vtimuchen-lab/dual-spark-4u/docs/drawings/panel_fp5.png

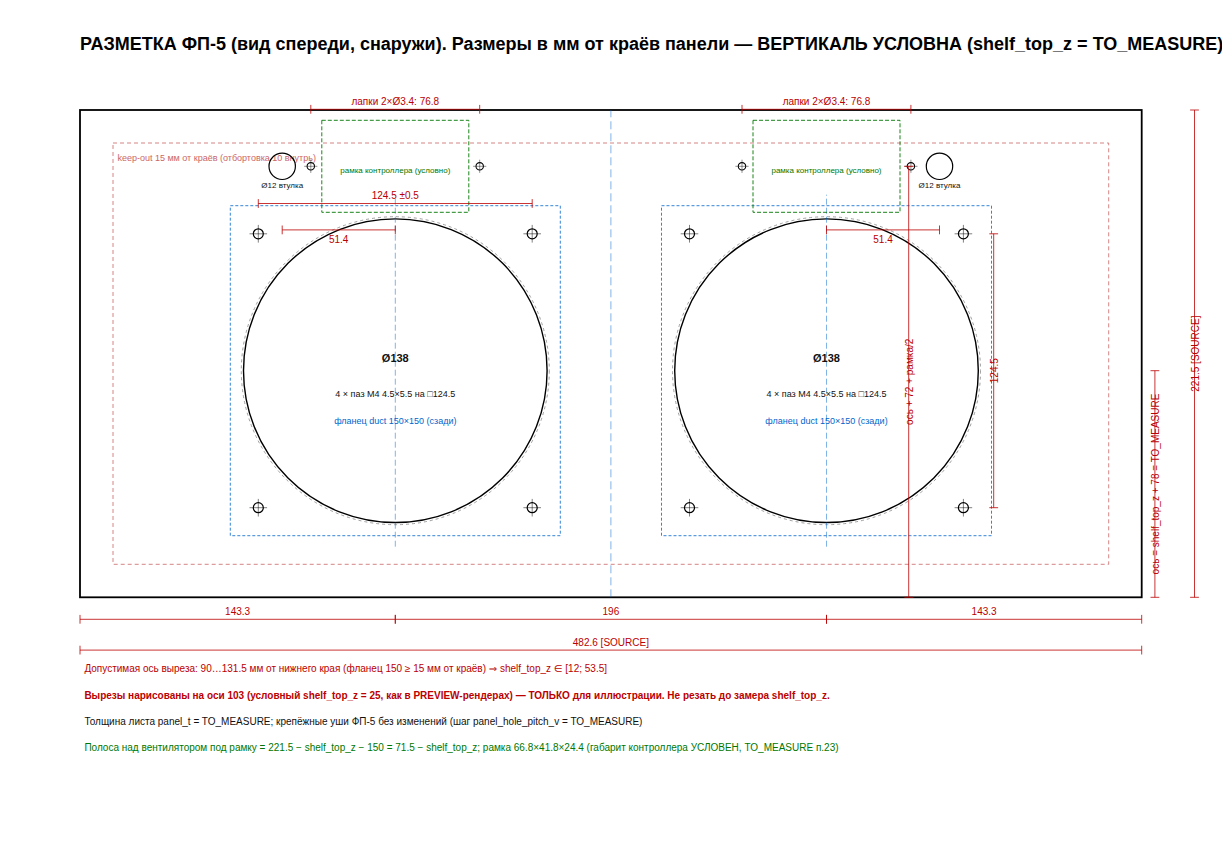
docs/drawings/panel_fp5.png
