vtimuchen-lab/dual-spark-4u/docs/drawings/side_view.png

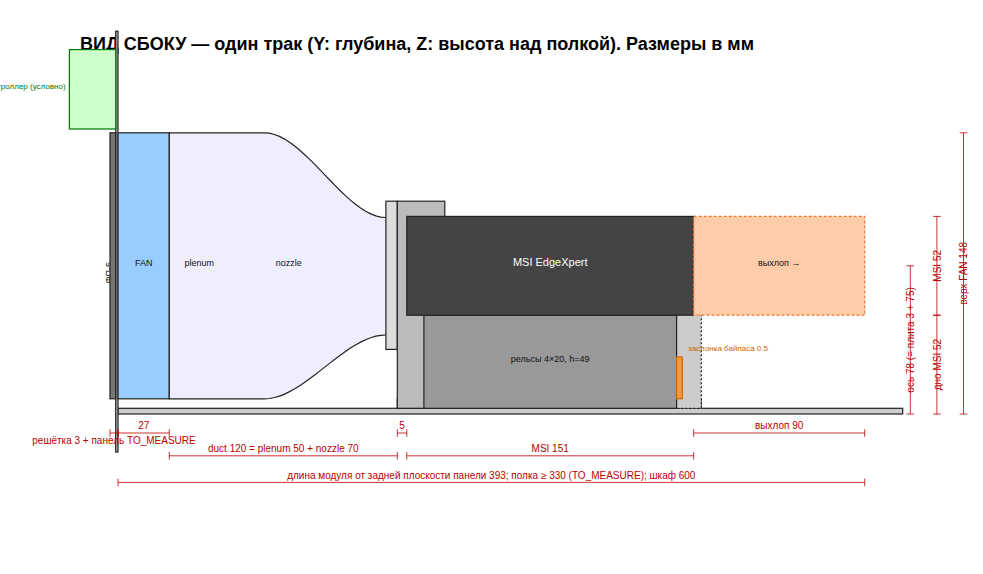
docs/drawings/side_view.png
