vtimuchen-lab/dual-spark-4u/docs/drawings/top_view.png

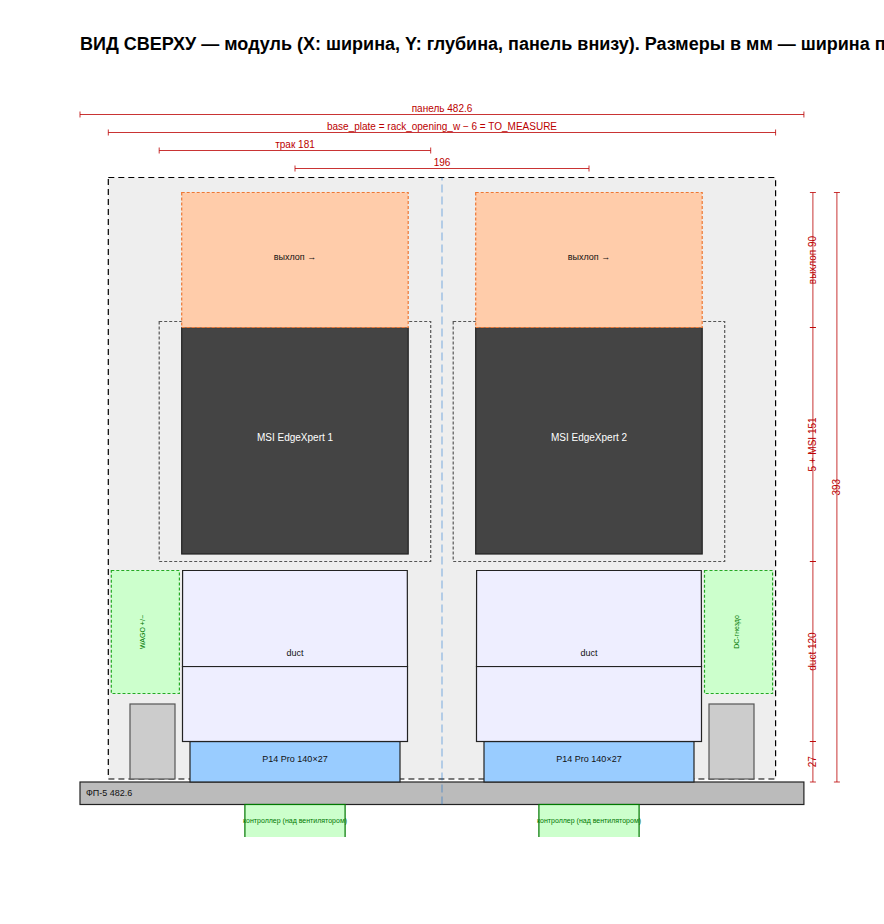
docs/drawings/top_view.png
