vtimuchen-lab/dual-spark-4u/docs/renders/duct_section_PREVIEW.png

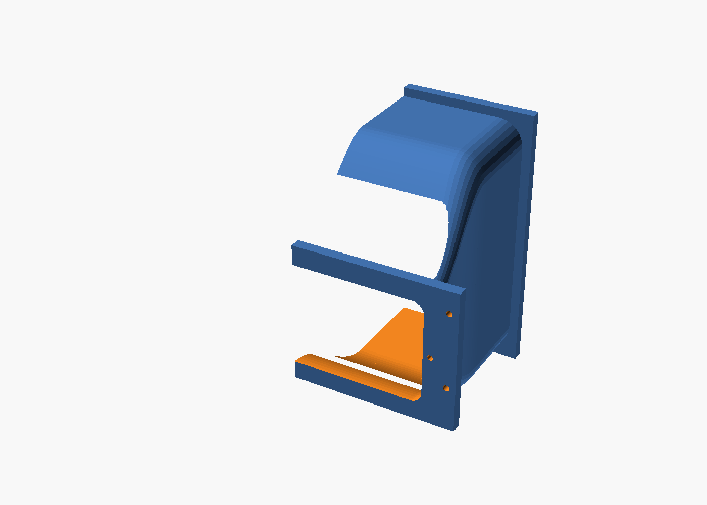
docs/renders/duct_section_PREVIEW.png
