vtimuchen-lab/dual-spark-4u/docs/renders/exploded_PREVIEW.png

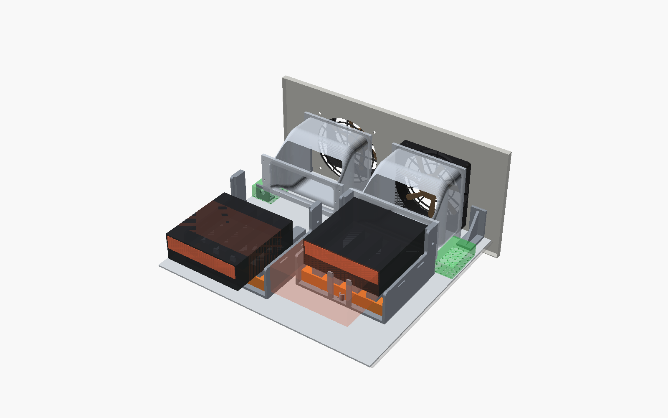
docs/renders/exploded_PREVIEW.png
