vtimuchen-lab/dual-spark-4u/docs/renders/holder_PREVIEW.png

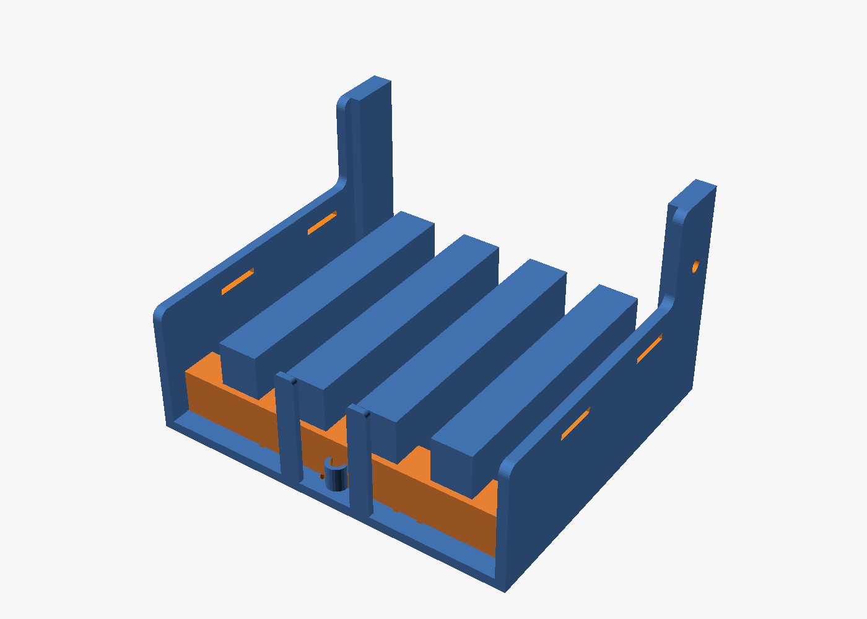
docs/renders/holder_PREVIEW.png
