vtimuchen-lab/dual-spark-4u/docs/renders/module_top_PREVIEW.png

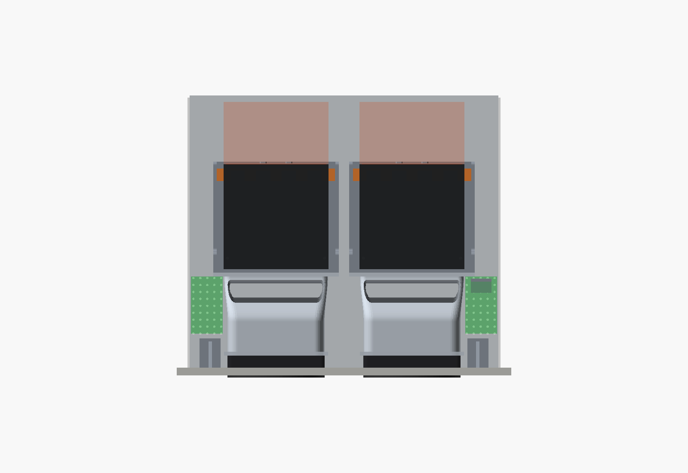
docs/renders/module_top_PREVIEW.png
