vtimuchen-lab/dual-spark-4u/docs/renders/panel_bracket_PREVIEW.png

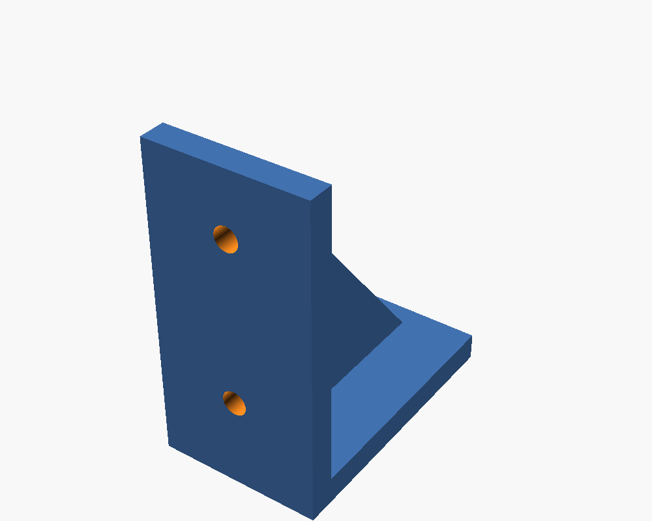
docs/renders/panel_bracket_PREVIEW.png
